Qutino/MacroPad1.0/Images/20230611_110757.jpg

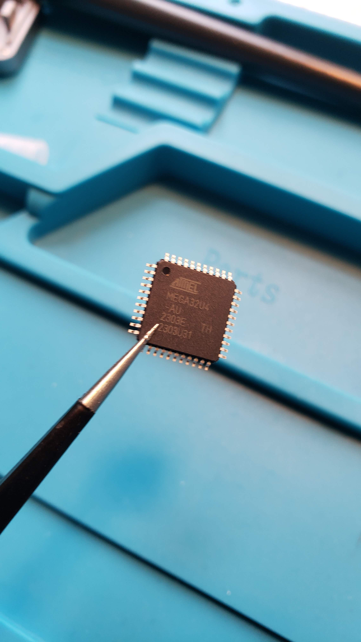
Images/20230611_110757.jpg
