Qutino/MacroPad1.0/Images/20230612_113359.jpg

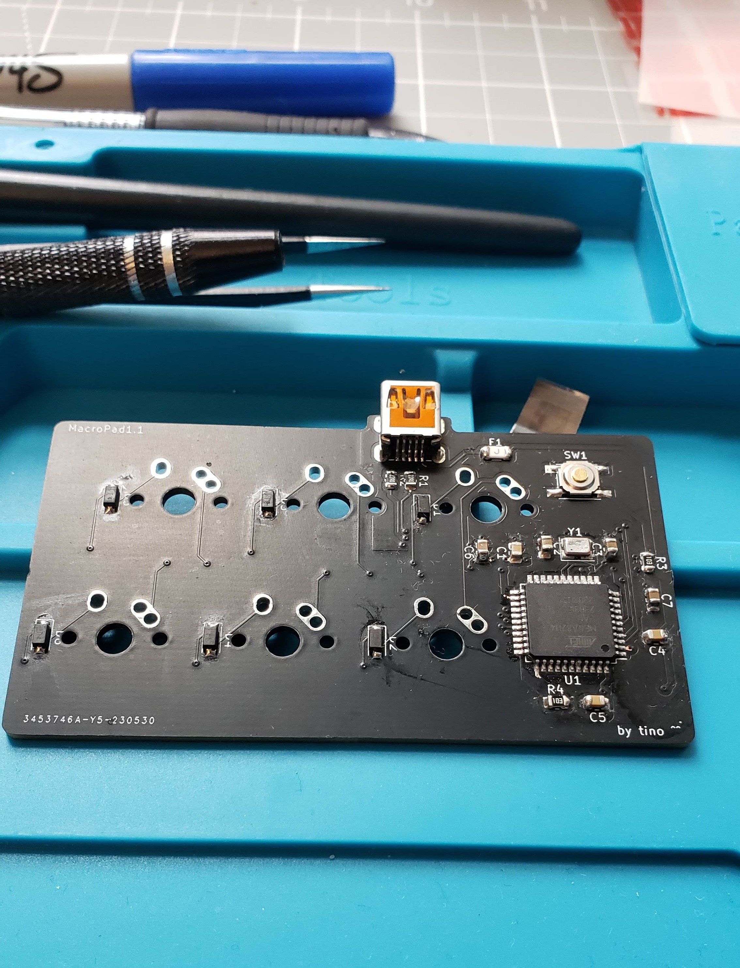
Images/20230612_113359.jpg
